RuAlMac/Clock_Project/Code/Acting/Clock_Cluster_Main/Serial_Monitor.ino

void printSerial(int message) {
  switch (message) {
    case 1:
      Serial.print("\n\n\n\n\n\n");
      Serial.print("**********Initializing Clock Cluster Main Board**********\n");
      break;
  }
  Serial.print("");
}
